LuckyResistor/SnowFlakeProject/SnowFlakeFirmware/src/Scene.hpp

//
// Snow Flake Project
// ---------------------------------------------------------------------------
// (c)2017-2019 by Lucky Resistor. See LICENSE for details.
// https://luckyresistor.me
//
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
#pragma once


#include "Frame.hpp"
#include "SceneData.hpp"


/// The base class for a single scene for the snow flake.
///
/// A scene is a single effect which is displayed on the LEDs of the snow flake.
///
class Scene
{
public:
	/// An enumeration to name all defined scenes in this firmware.
	///
	enum Name : uint8_t {
		Black = 0,
		IceSparkle,
		SkyWithStars,
		Waves,
		Circles,
		Rain,
		SimpleShift,
		SimpleRotation,
		SimpleDiagonal,
		SimpleFlash,
		SimpleRandomParticle,
		SimpleRandomFlicker,
		User,
	};
	
public:
	/// Function pointer to the initialization function.
	///
	typedef void(*InitFn)(SceneData*, uint8_t entropy);
	
	/// Function pointer to the `getFrame` function.
	///
	typedef Frame(*GetFrameFn)(SceneData*, FrameIndex frameIndex);	

public:
	/// Create a empty scene.
	///
	/// This is a non functional scene, used as placeholder.
	///
	Scene();
	
	/// Create a new scene.
	///
	/// @param frameCount The frame count for this scene. Has to be >0.
	/// @param initSceneFn The function to initialize the scene data.
	/// @param getFrameFn The function to get a new frame for the scene.
	///
	Scene(FrameIndex frameCount, InitFn initFn, GetFrameFn getFrameFn);
	
	/// Copy constructor
	///
	Scene(const Scene &copy);
	
	/// Assign operator.
	///
	const Scene& operator=(const Scene &assign);
	
public:
	/// Get the frame count.
	///
	inline FrameIndex getFrameCount() const { return _frameCount; }

	/// Initialize the given scene data.
	///
	void init(SceneData *data, uint8_t entropy);
	
	/// Get a frame for this scene.
	///
	Frame getFrame(SceneData *data, FrameIndex frameIndex);
	
private:
	FrameIndex _frameCount; ///< The frame count for this scene.
	InitFn _initFn; ///< The function to initialize the scene data.
	GetFrameFn _getFrameFn; ///< The function to get a new frame for this scene.
};
