LuckyResistor/SnowFlakeProject/SnowFlakeFirmware/src/ShiftingMap.hpp

//
// Snow Flake Project
// ---------------------------------------------------------------------------
// (c)2017 by Lucky Resistor. See LICENSE for details.
// https://luckyresistor.me
//
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
#pragma once


#include "SceneData.hpp"


/// This helper class contains the calculations for a LED map with a random rotation.
///
/// @tparam dataOffset The offset the the scene data where to store the rotation and
///   range data. This class uses two entries in the scene data.
///
template<uint16_t dataOffset = 0>
class ShiftingMap
{
public:
	/// Create a new shifting map instance.
	///
	/// @param ledMap The pointer to the ledMap to use.
	/// @param range The range for the displayed values on the map.
	/// @param rotationSceneDataIndex The index in the scene data int8 array where to store the rotation value.
	///
	constexpr ShiftingMap(const Fixed16* const ledMap)
		: _ledMap(ledMap)
	{
	}

public:
	/// Get the offset in the `int8` array of the scene data for the rotation.
	///
	inline uint16_t getRotationInt8Offset() const {
		return (dataOffset+1)*4;
	}
	
	/// Get the offset in the `fixed16` array for the range value.
	///
	inline uint16_t getRangeOffset() const {
		return dataOffset;
	}
	
	/// Initialize the scene data for the shifting map.
	///
	void initialize(SceneData *sceneData, uint8_t rotation, const Fixed16 range) const {
		rotation &= 0x7;
		if (rotation > 5) {
			rotation -= 6;
		}
		sceneData->int8[getRotationInt8Offset()] = rotation;
		sceneData->fixed16[getRangeOffset()] = range;
	}

	/// Get the wrapped position for a given frame.
	///
	PixelValue getPositionWrapped(SceneData *sceneData, uint8_t pixelIndex, FrameIndex frameCount, FrameIndex frameIndex) const
	{
		const auto normal = PixelValue::normalFromRange<FrameIndex>(0, frameCount, frameIndex);
		const auto rotation = sceneData->int8[getRotationInt8Offset()];
		const auto pixelIndexAfterRotation = LedMaps::cIndexRotation[rotation][pixelIndex];
		const auto range = sceneData->fixed16[getRangeOffset()];
		const auto mapShift = (_ledMap[pixelIndexAfterRotation] * range);
		const auto result = PixelValue(normal - mapShift);
		return result.wrapped();
	}
	
private:
	const Fixed16* const _ledMap;
};
